gowenrw/sailor_moon_badge/art/inspiration/741863f426b0aff89c0e56212ef1270b.jpg

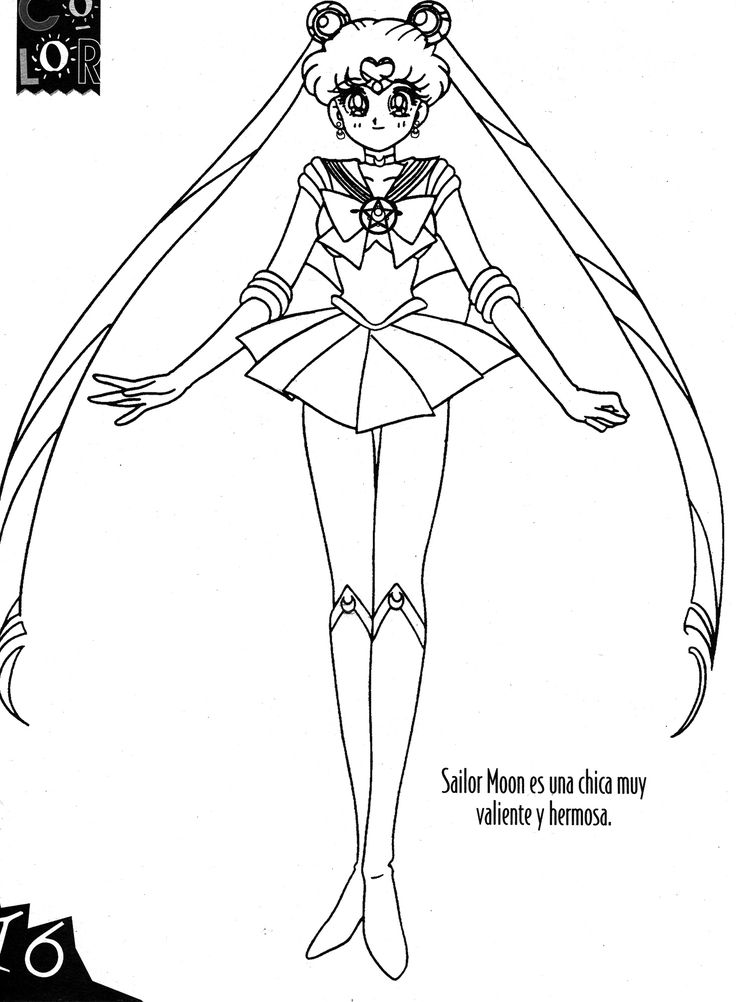
art/inspiration/741863f426b0aff89c0e56212ef1270b.jpg
