gowenrw/sailor_moon_badge/art/inspiration/3416023.png

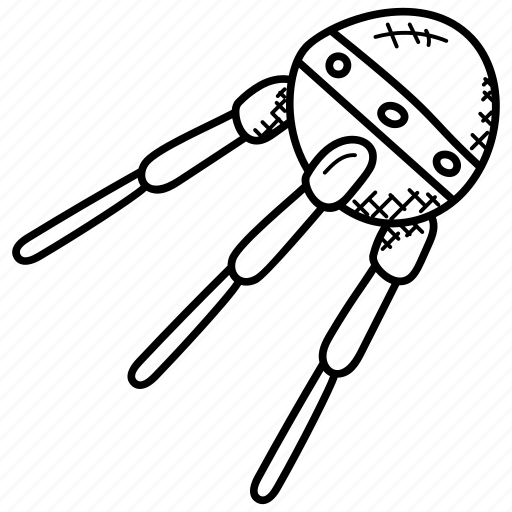
art/inspiration/3416023.png
