gowenrw/sailor_moon_badge/art/inspiration/aniyuki-sailor-moon-coloring-pages-17.jpg

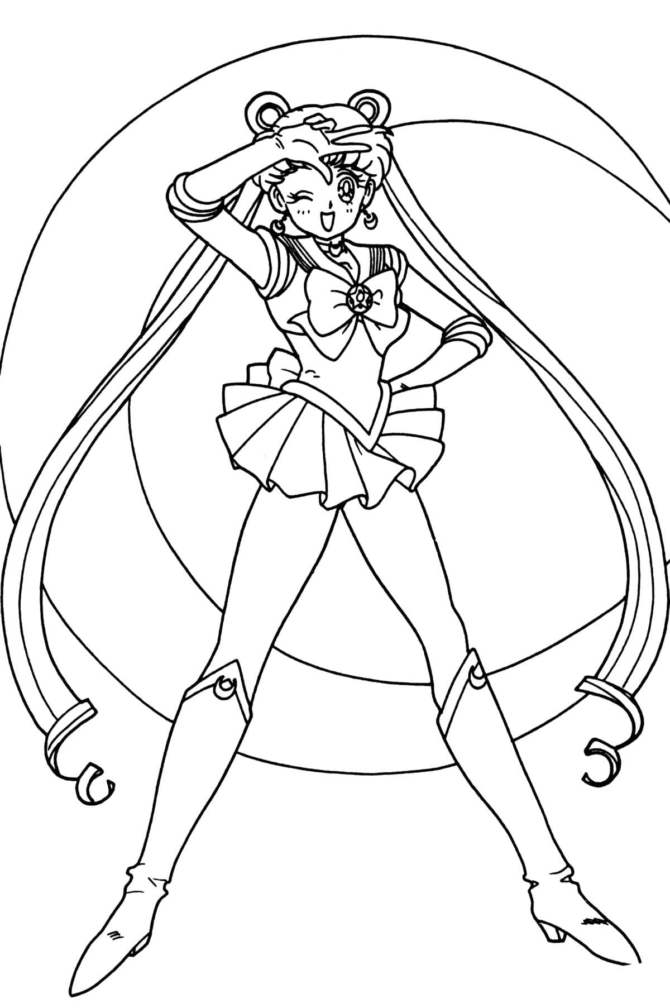
art/inspiration/aniyuki-sailor-moon-coloring-pages-17.jpg
