gowenrw/sailor_moon_badge/art/inspiration/earth.JPG

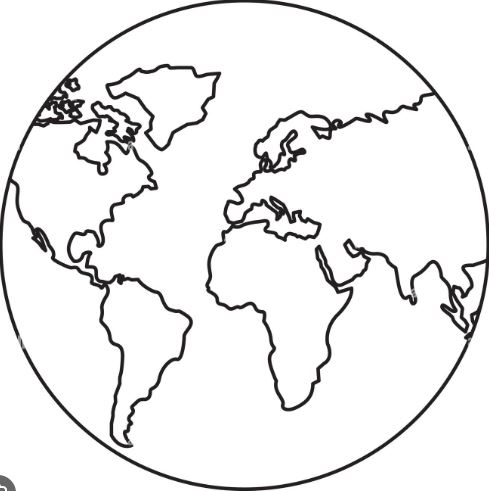
art/inspiration/earth.JPG
