gowenrw/sailor_moon_badge/art/inspiration/heart_wings.JPG

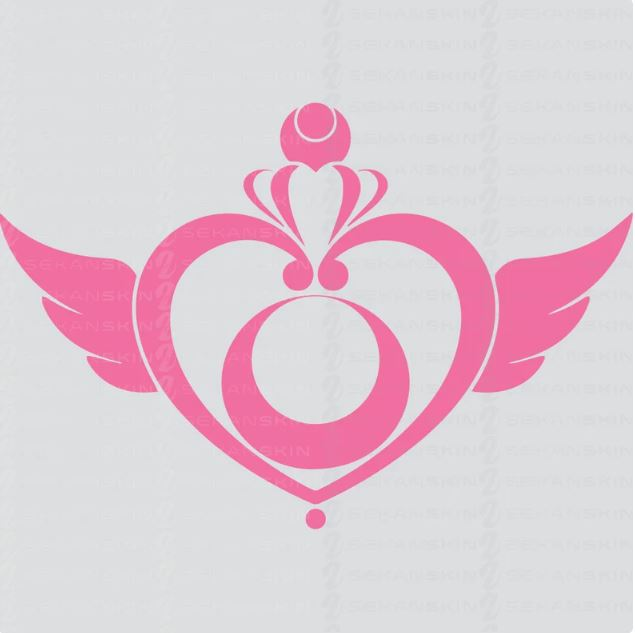
art/inspiration/heart_wings.JPG
