gowenrw/sailor_moon_badge/art/inspiration/il_fullxfull.png

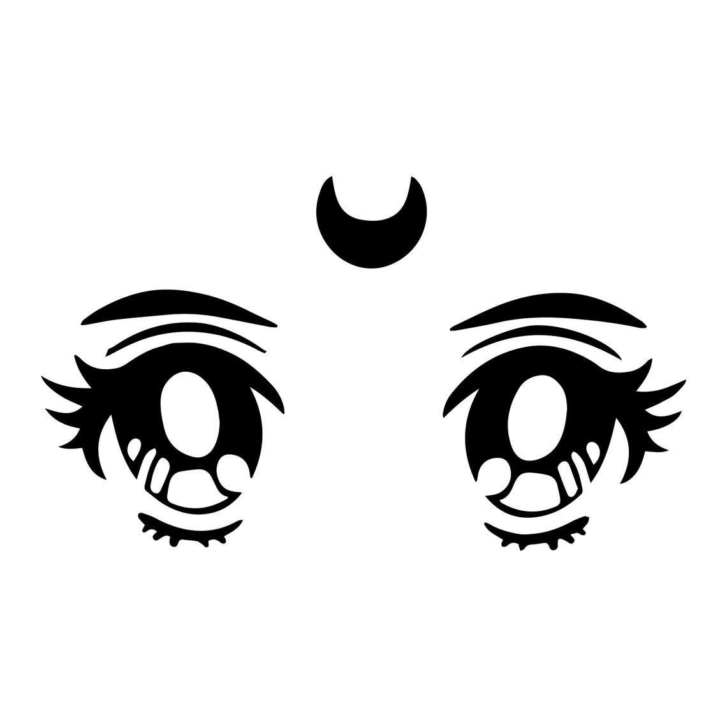
art/inspiration/il_fullxfull.png
