gowenrw/sailor_moon_badge/art/inspiration/Raskrasil.com-Sailor-Moon-2.jpg

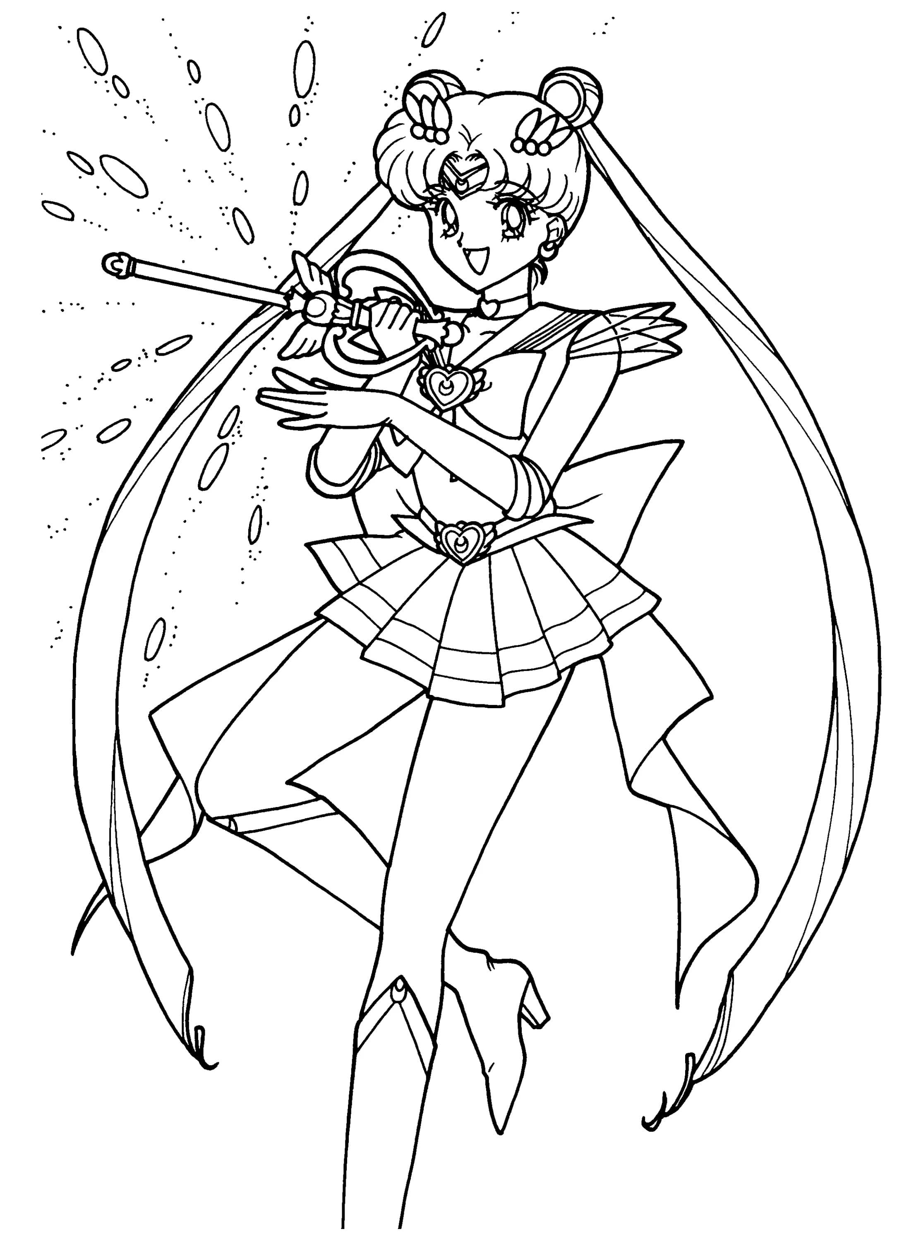
art/inspiration/Raskrasil.com-Sailor-Moon-2.jpg
