gowenrw/sailor_moon_badge/art/inspiration/sailor_moon_sketch_by_art_gives_me_purpose_dey1yrh-fullview.jpg

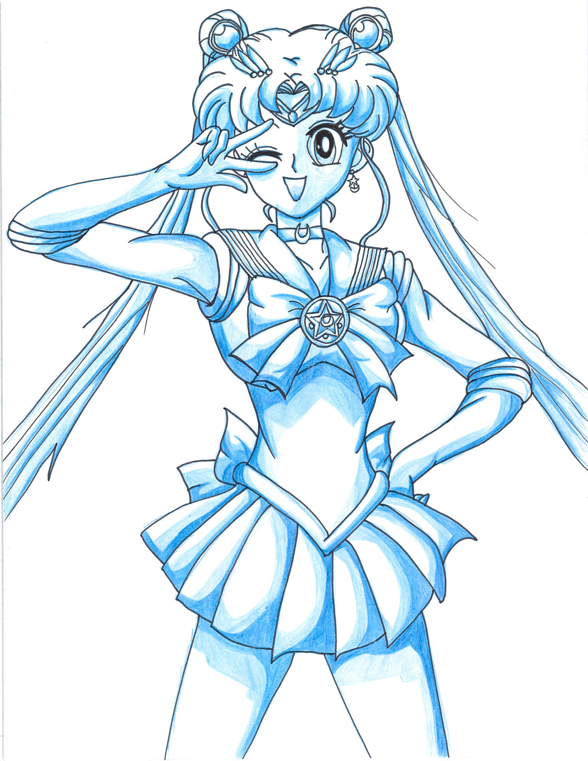
art/inspiration/sailor_moon_sketch_by_art_gives_me_purpose_dey1yrh-fullview.jpg
