gowenrw/sailor_moon_badge/art/inspiration/satellite.png

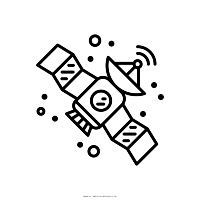
art/inspiration/satellite.png
