gowenrw/sailor_moon_badge/art/Sailor_Moon-1-maskb-01.jpg

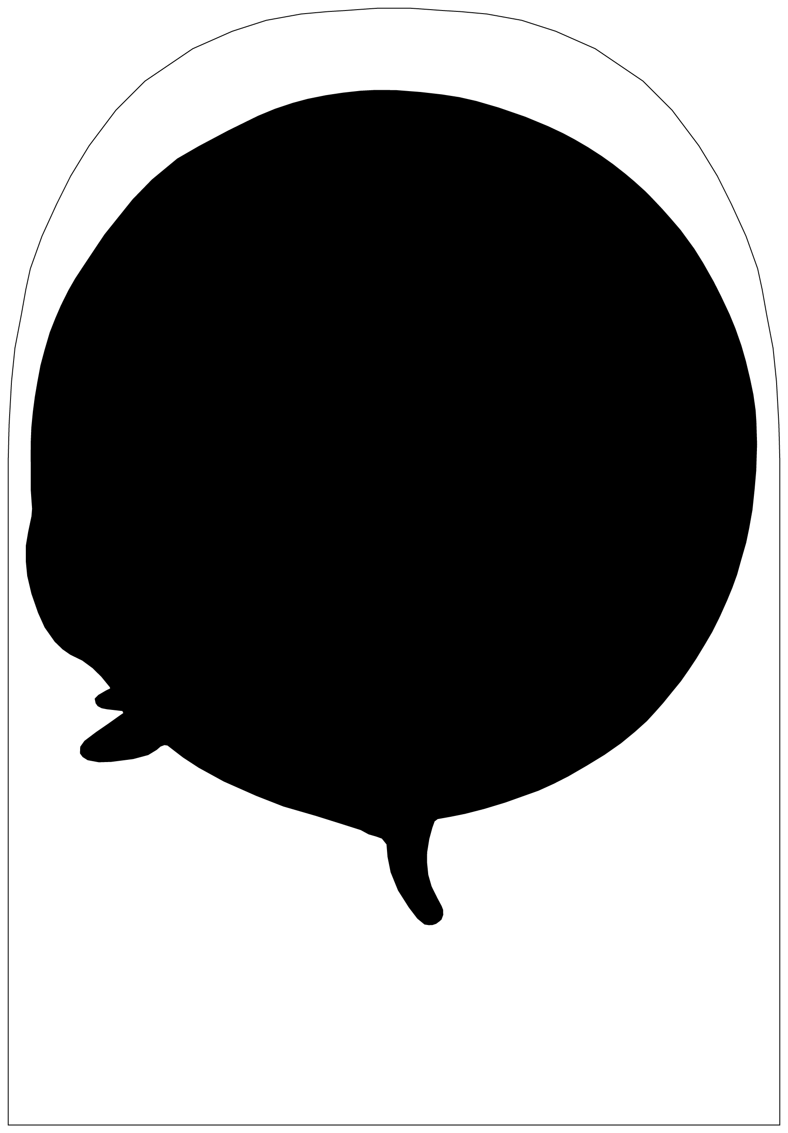
art/Sailor_Moon-1-maskb-01.jpg
