gowenrw/sailor_moon_badge/art/Sailor_Moon-1-maskf-01.jpg

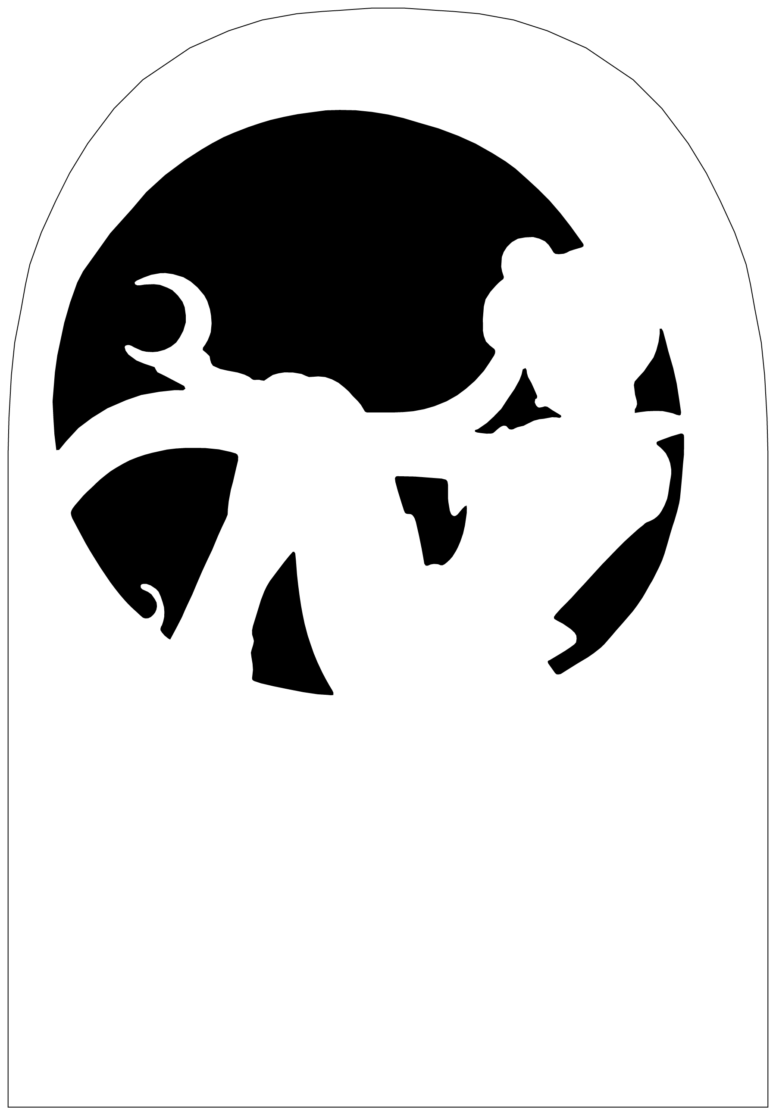
art/Sailor_Moon-1-maskf-01.jpg
