gowenrw/sailor_moon_badge/art/Sailor_Moon-2-bottom-01.jpg

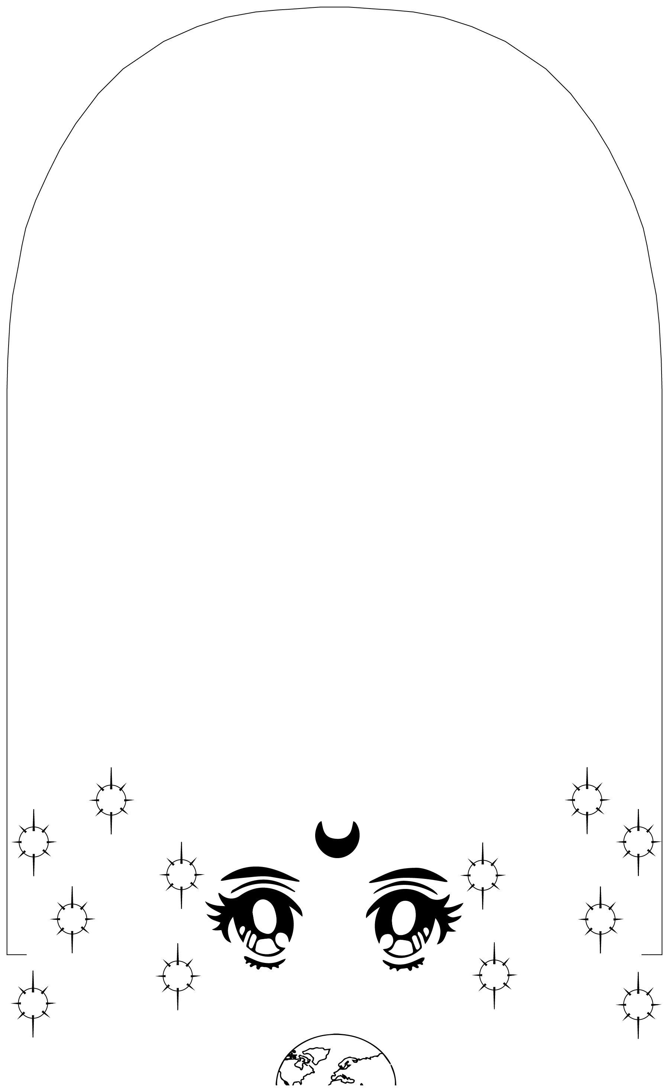
art/Sailor_Moon-2-bottom-01.jpg
