gowenrw/sailor_moon_badge/eda/sailor_moon/gerber/PCBWAY-DrillSettings.JPG

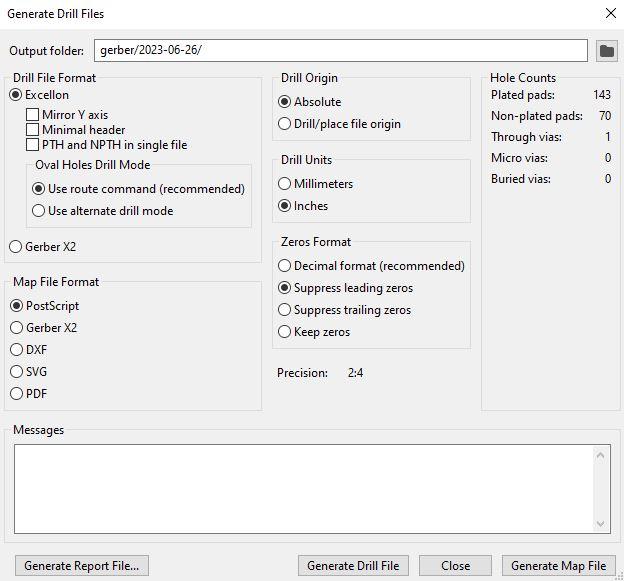
eda/sailor_moon/gerber/PCBWAY-DrillSettings.JPG
