gowenrw/sailor_moon_badge/eda/sailor_moon/gerber/PCBWAY-GerberSetting.JPG

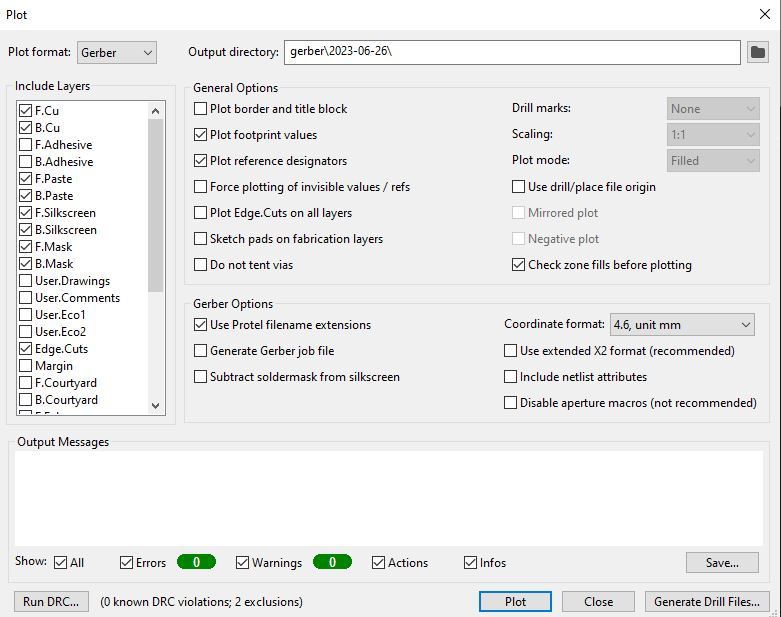
eda/sailor_moon/gerber/PCBWAY-GerberSetting.JPG
