gowenrw/sailor_moon_badge/eda/sailor_moon/snapshots/sailor_moon_3d_back.jpg

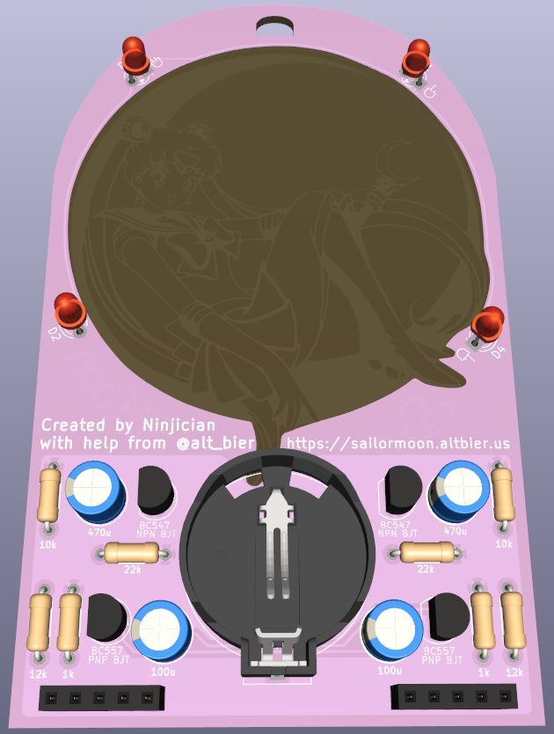
eda/sailor_moon/snapshots/sailor_moon_3d_back.jpg
