gowenrw/sailor_moon_badge/eda/sailor_moon/snapshots/sailor_moon_3d_front.jpg

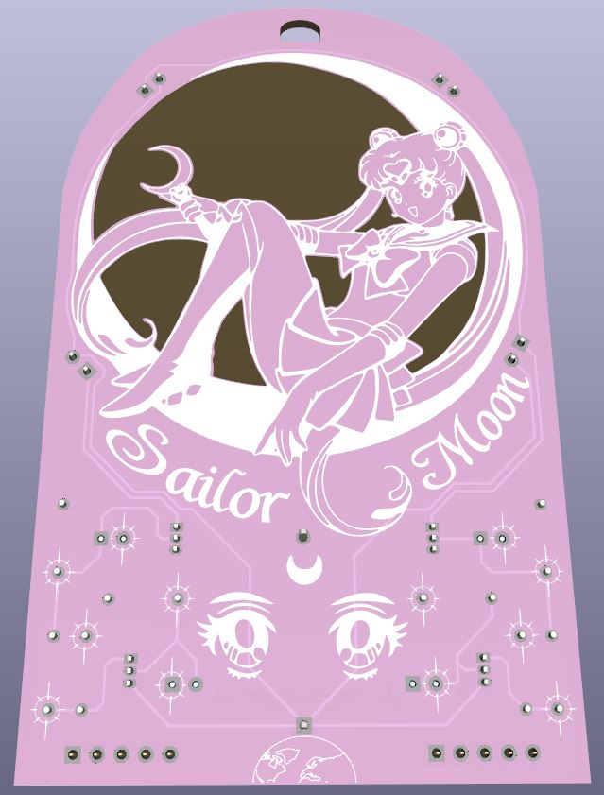
eda/sailor_moon/snapshots/sailor_moon_3d_front.jpg
