gowenrw/sailor_moon_badge/eda/sailor_moon/3d_models/PinHeader_1x02_P2.54mm_Horizontal.step

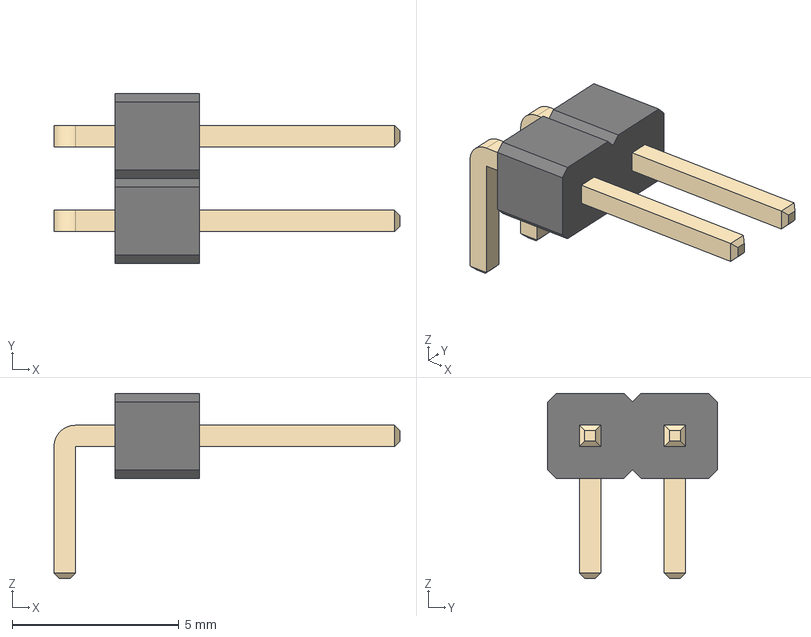
[picture p48: CAD file, 2023-08-03]
eda/sailor_moon/3d_models/PinHeader_1x02_P2.54mm_Horizontal.step
10.4 x 5.08 x 5.54 mm
