gowenrw/sailor_moon_badge/eda/sailor_moon/3d_models/LED_0805_2012Metric_Castellated.step

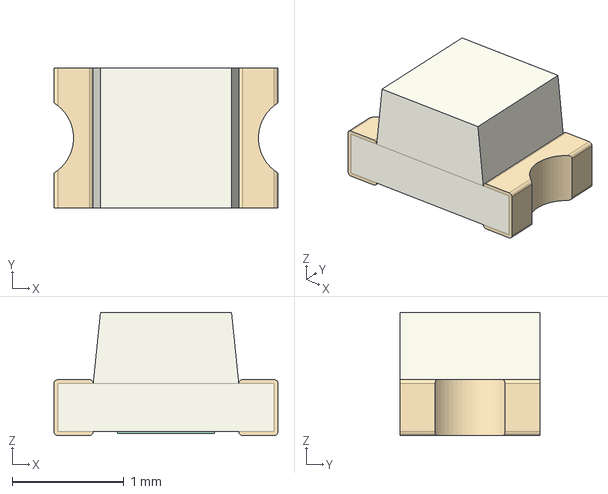
[picture p52: CAD file, 2023-08-03]
eda/sailor_moon/3d_models/LED_0805_2012Metric_Castellated.step
2.00 x 1.25 x 1.10 mm
