gowenrw/sailor_moon_badge/eda/sailor_moon/3d_models/R_Axial_DIN0207_L6.3mm_D2.5mm_P7.62mm_Horizontal.step

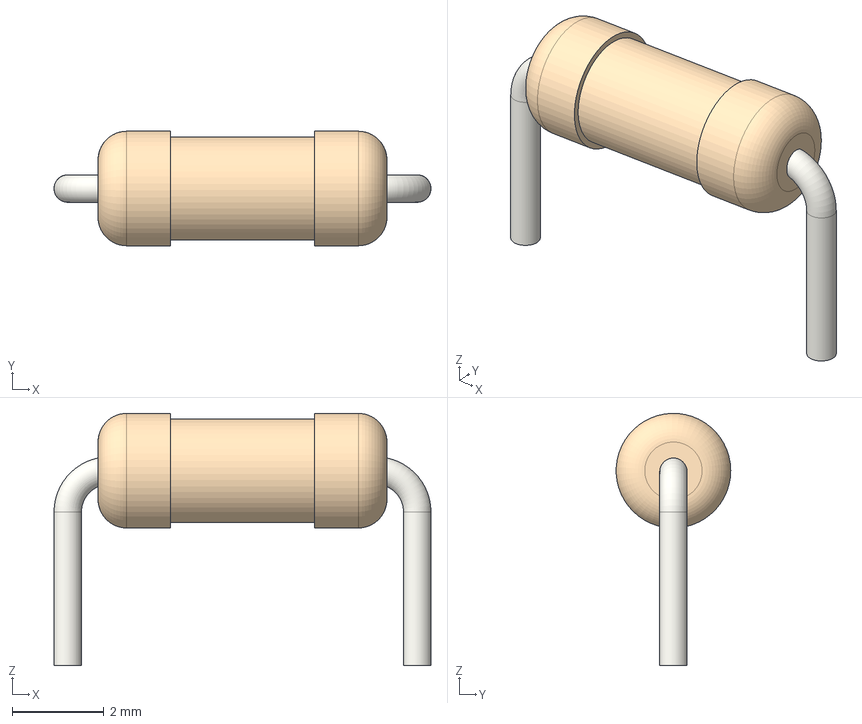
[picture p54: CAD file, 2023-08-03]
eda/sailor_moon/3d_models/R_Axial_DIN0207_L6.3mm_D2.5mm_P7.62mm_Horizontal.step
8.22 x 2.50 x 5.50 mm
