gowenrw/sailor_moon_badge/eda/sailor_moon/3d_models/LED_D5.0mm.step

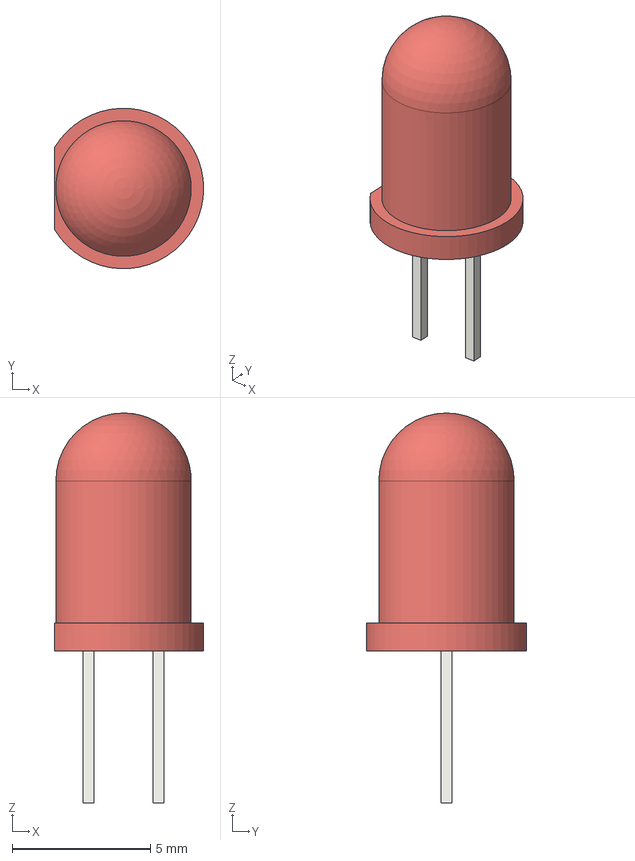
[picture p56: CAD file, 2023-08-03]
eda/sailor_moon/3d_models/LED_D5.0mm.step
5.40 x 5.79 x 14.1 mm
