gowenrw/sailor_moon_badge/eda/sailor_moon/3d_models/R_Axial_DIN0204_L3.6mm_D1.6mm_P5.08mm_Horizontal.step

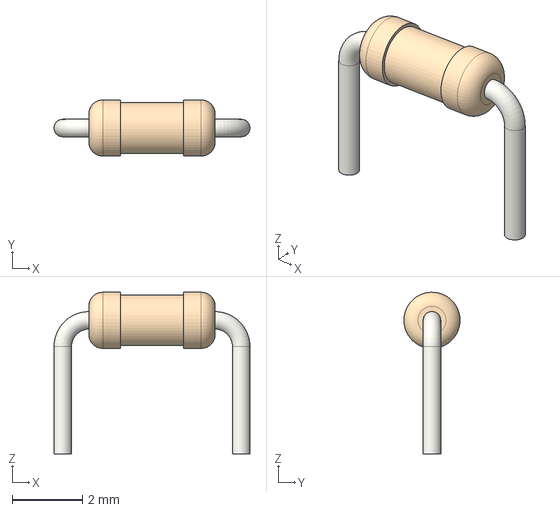
[picture p58: CAD file, 2023-08-03]
eda/sailor_moon/3d_models/R_Axial_DIN0204_L3.6mm_D1.6mm_P5.08mm_Horizontal.step
5.58 x 1.60 x 4.60 mm
