gowenrw/sailor_moon_badge/eda/sailor_moon/3d_models/CUI_PXO7803-500-M-TR.step

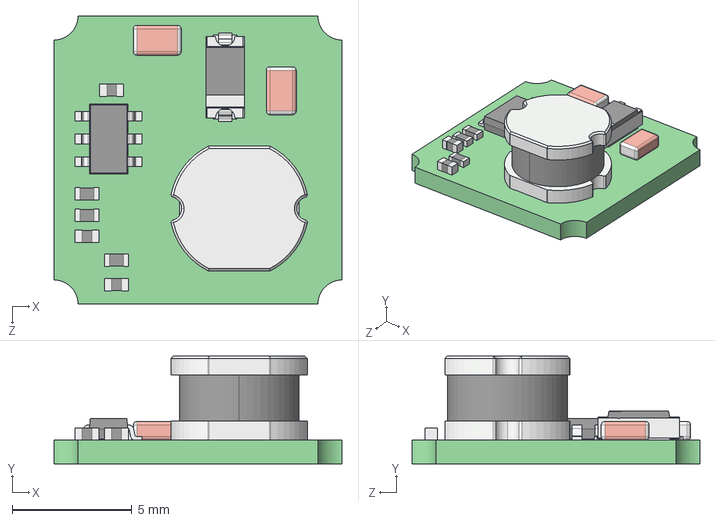
[picture p61: CAD file, 2023-08-03]
eda/sailor_moon/3d_models/CUI_PXO7803-500-M-TR.step
12.0 x 4.50 x 12.0 mm
