gowenrw/sailor_moon_badge/eda/sailor_moon/3d_models/PinSocket_1x04_P2.54mm_Horizontal.step

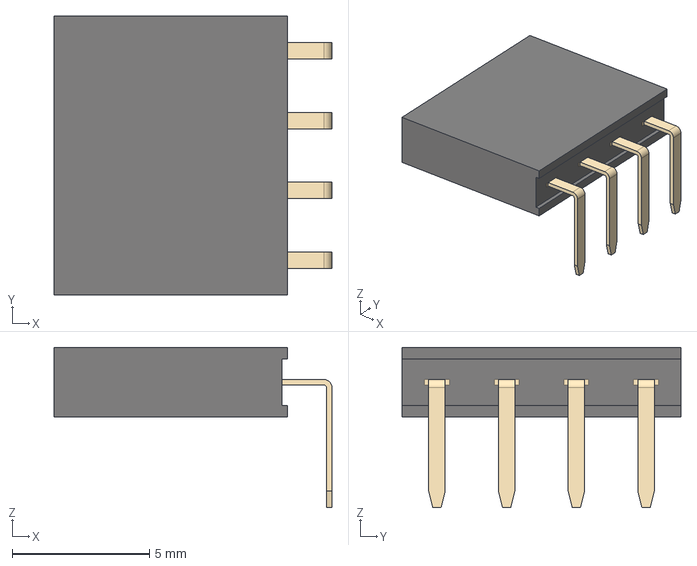
[picture p65: CAD file, 2023-08-03]
eda/sailor_moon/3d_models/PinSocket_1x04_P2.54mm_Horizontal.step
10.1 x 10.2 x 5.84 mm
