gowenrw/sailor_moon_badge/eda/sailor_moon/3d_models/C_1206_3216Metric.step

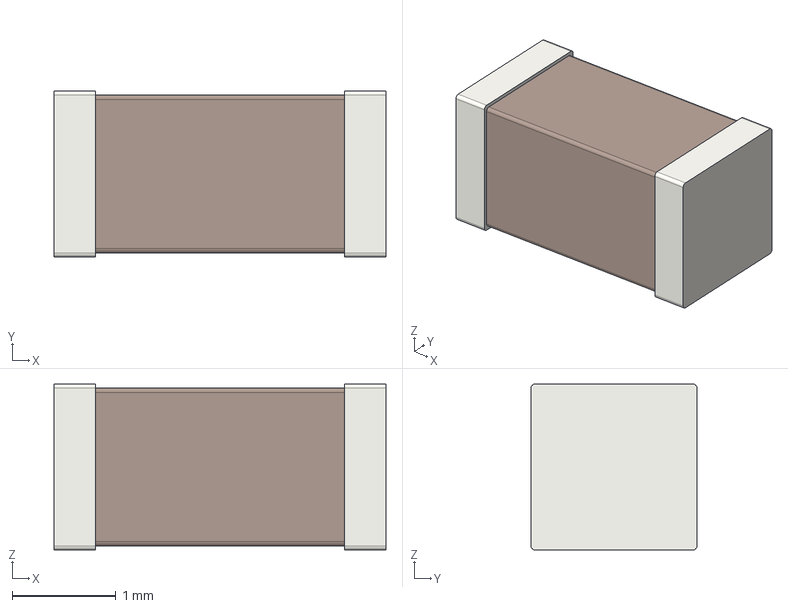
[picture p66: CAD file, 2023-08-03]
eda/sailor_moon/3d_models/C_1206_3216Metric.step
3.20 x 1.60 x 1.60 mm
