gowenrw/sailor_moon_badge/eda/sailor_moon/3d_models/LED_D3.0mm.step

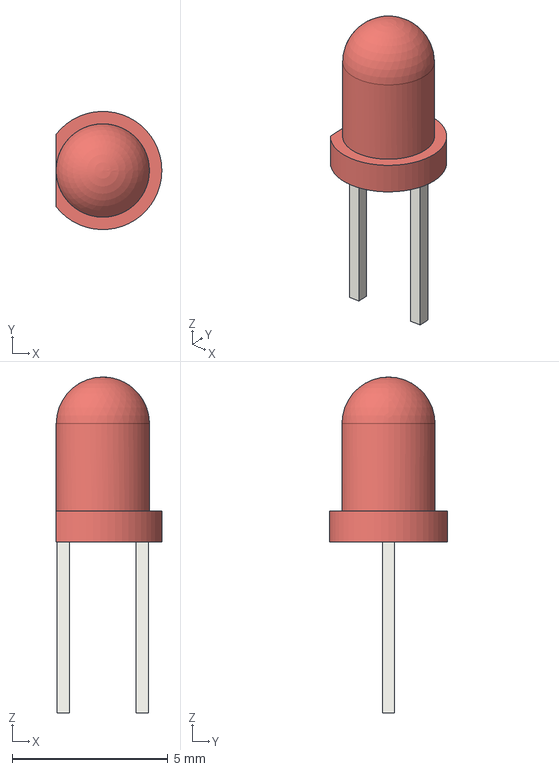
[picture p68: CAD file, 2023-08-03]
eda/sailor_moon/3d_models/LED_D3.0mm.step
3.40 x 3.80 x 10.8 mm
