gowenrw/sailor_moon_badge/eda/sailor_moon/3d_models/SW_SPDT_PCM12.step

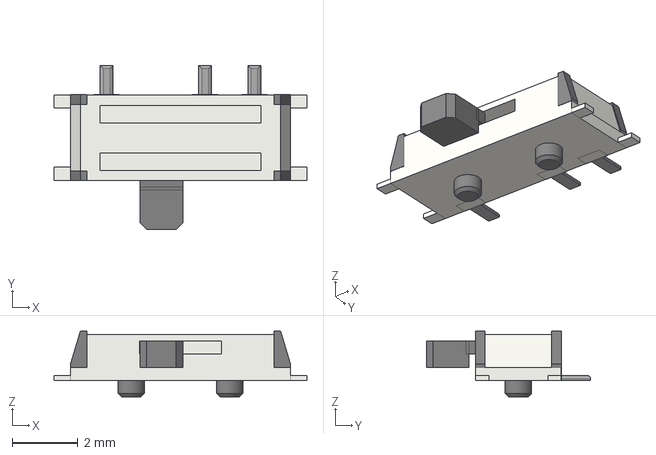
[picture p70: CAD file, 2023-08-03]
eda/sailor_moon/3d_models/SW_SPDT_PCM12.step
7.70 x 5.00 x 2.00 mm
