gowenrw/sailor_moon_badge/eda/sailor_moon/3d_models/RJ45_Amphenol_RJHSE-5080-56544.STEP

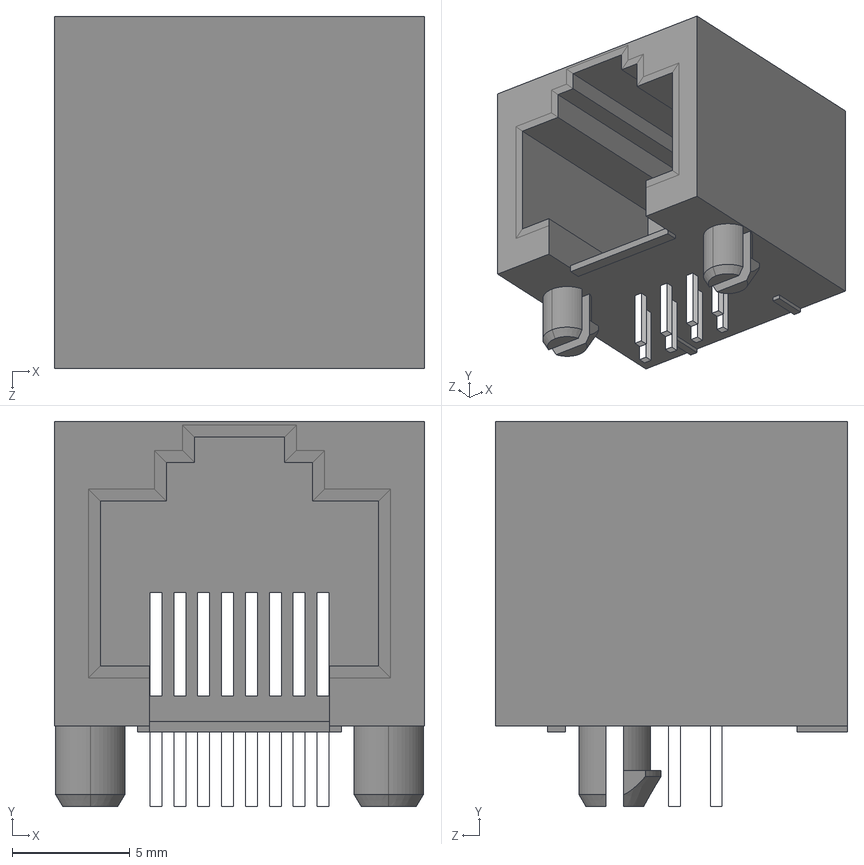
[picture p72: CAD file, 2023-08-03]
eda/sailor_moon/3d_models/RJ45_Amphenol_RJHSE-5080-56544.STEP
15.7 x 16.4 x 15.0 mm
