gowenrw/sailor_moon_badge/eda/sailor_moon/3d_models/Battery_Holder_CR2032_BS-2-1.stp

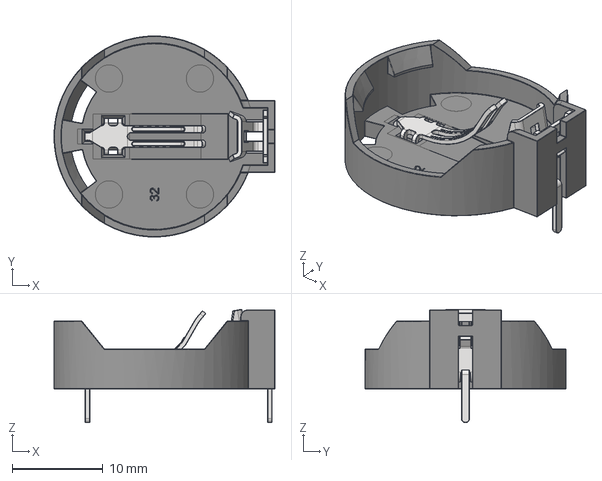
[picture p73: CAD file, 2023-08-03]
eda/sailor_moon/3d_models/Battery_Holder_CR2032_BS-2-1.stp
24.3 x 22.1 x 12.5 mm
