gowenrw/sailor_moon_badge/eda/sailor_moon/3d_models/TO-92_Inline.step

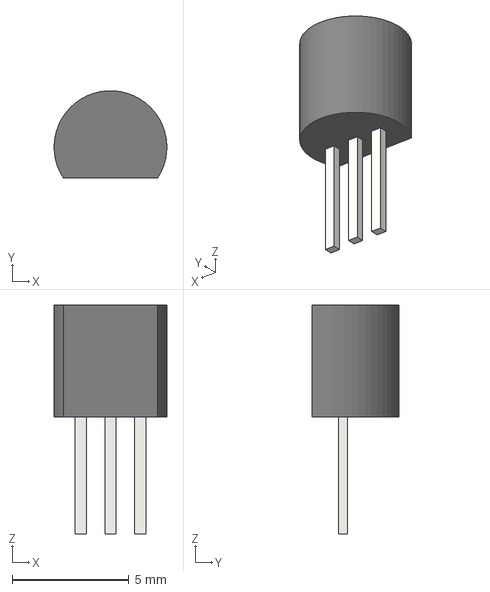
[picture p78: CAD file, 2023-08-03]
eda/sailor_moon/3d_models/TO-92_Inline.step
4.83 x 3.74 x 9.80 mm
