gowenrw/sailor_moon_badge/eda/sailor_moon/3d_models/TS2306A.step

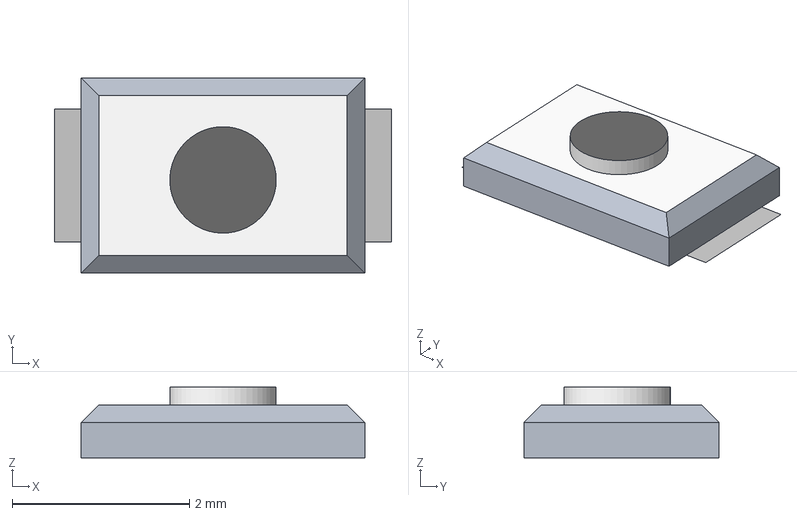
[picture p79: CAD file, 2023-08-03]
eda/sailor_moon/3d_models/TS2306A.step
3.80 x 2.20 x 0.8 mm
Plane
