gowenrw/sailor_moon_badge/eda/sailor_moon/3d_models/PinSocket_1x03_P2.54mm_Vertical.step

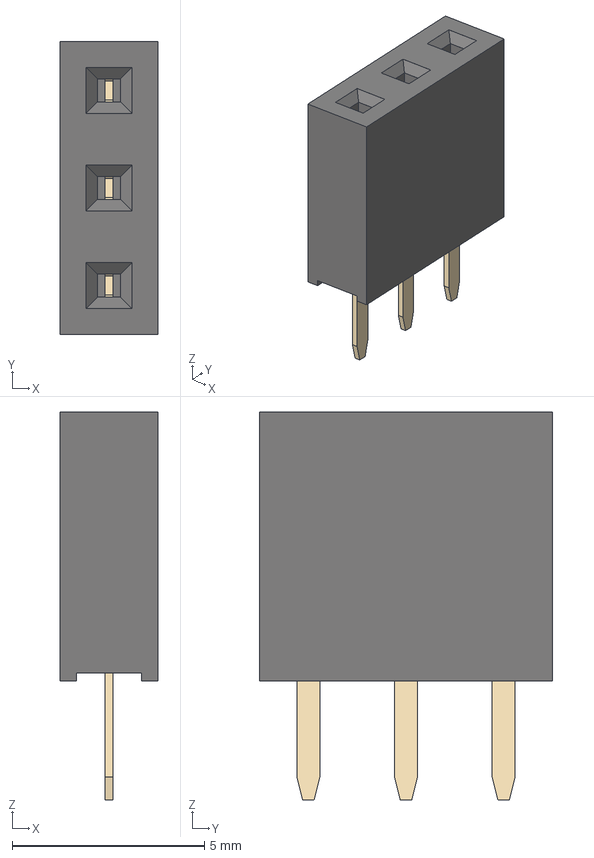
[picture p83: CAD file, 2023-08-03]
eda/sailor_moon/3d_models/PinSocket_1x03_P2.54mm_Vertical.step
2.54 x 7.62 x 10.1 mm
