gowenrw/sailor_moon_badge/eda/sailor_moon/3d_models/Battery_Holder_3xAAA_Simple.step

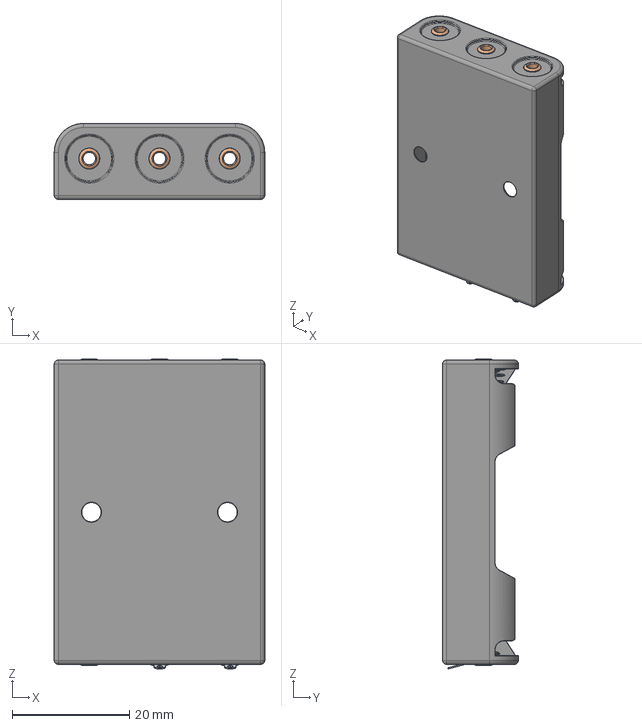
[picture p85: CAD file, 2023-08-03]
eda/sailor_moon/3d_models/Battery_Holder_3xAAA_Simple.step
36.0 x 13.0 x 53.0 mm
