gowenrw/sailor_moon_badge/eda/sailor_moon/3d_models/PinSocket_1x20_P2.54mm_Horizontal.step

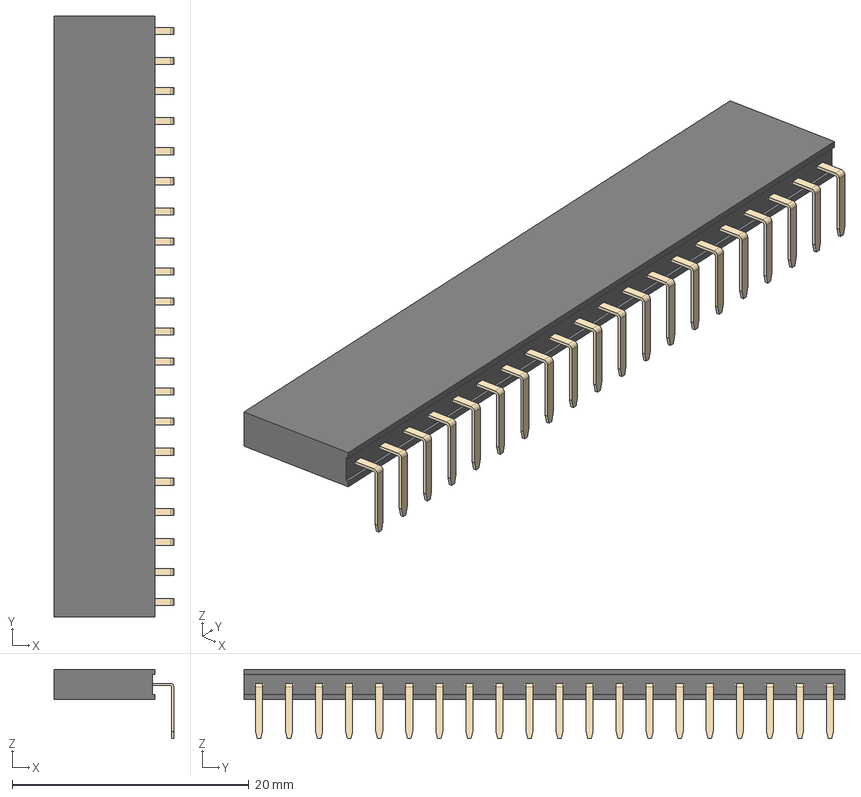
[picture p89: CAD file, 2023-08-03]
eda/sailor_moon/3d_models/PinSocket_1x20_P2.54mm_Horizontal.step
10.1 x 50.8 x 5.84 mm
