gowenrw/sailor_moon_badge/eda/sailor_moon/3d_models/LED_1206_3216Metric_Castellated.step

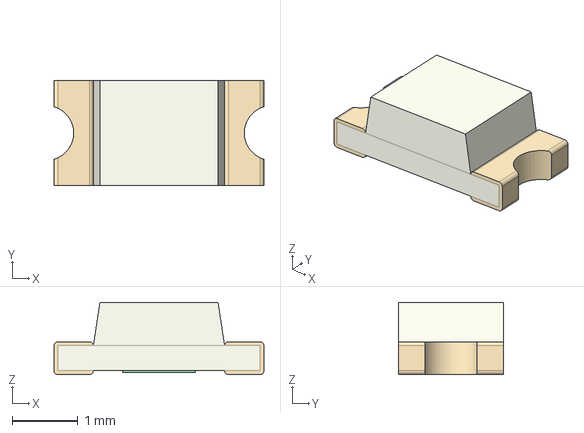
[picture p90: CAD file, 2023-08-03]
eda/sailor_moon/3d_models/LED_1206_3216Metric_Castellated.step
3.20 x 1.60 x 1.10 mm
