gowenrw/sailor_moon_badge/eda/sailor_moon/3d_models/PinHeader_1x09_P2.54mm_Vertical.step

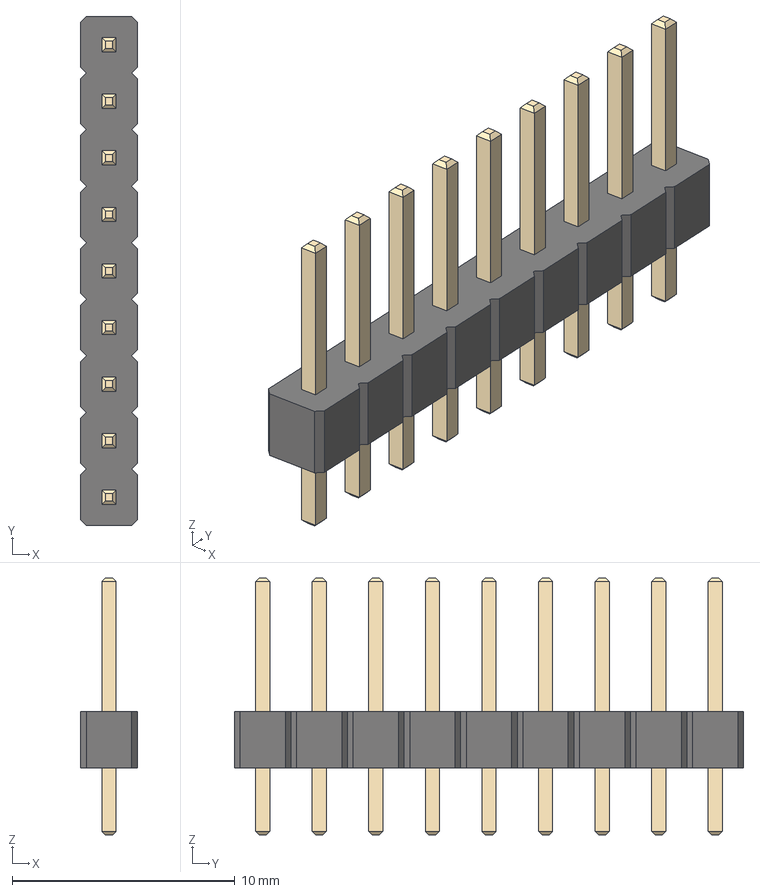
[picture p94: CAD file, 2023-08-03]
eda/sailor_moon/3d_models/PinHeader_1x09_P2.54mm_Vertical.step
2.54 x 22.9 x 11.5 mm
