gowenrw/sailor_moon_badge/eda/sailor_moon/3d_models/USB_Micro-B_Molex_47346-0001.step

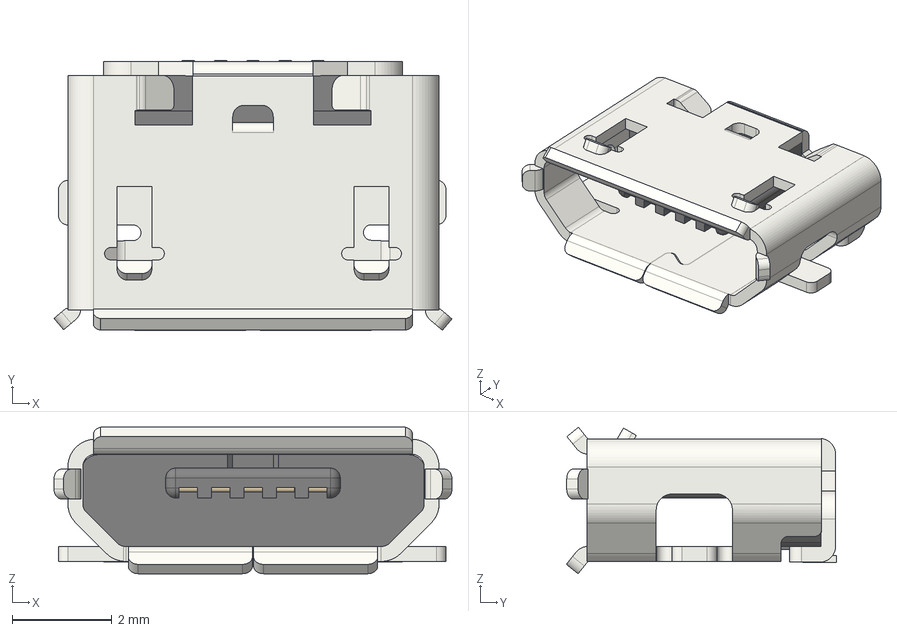
[picture p98: CAD file, 2023-08-03]
eda/sailor_moon/3d_models/USB_Micro-B_Molex_47346-0001.step
7.98 x 5.42 x 2.94 mm
