gowenrw/sailor_moon_badge/eda/sailor_moon/3d_models/LED_D8.0mm.step

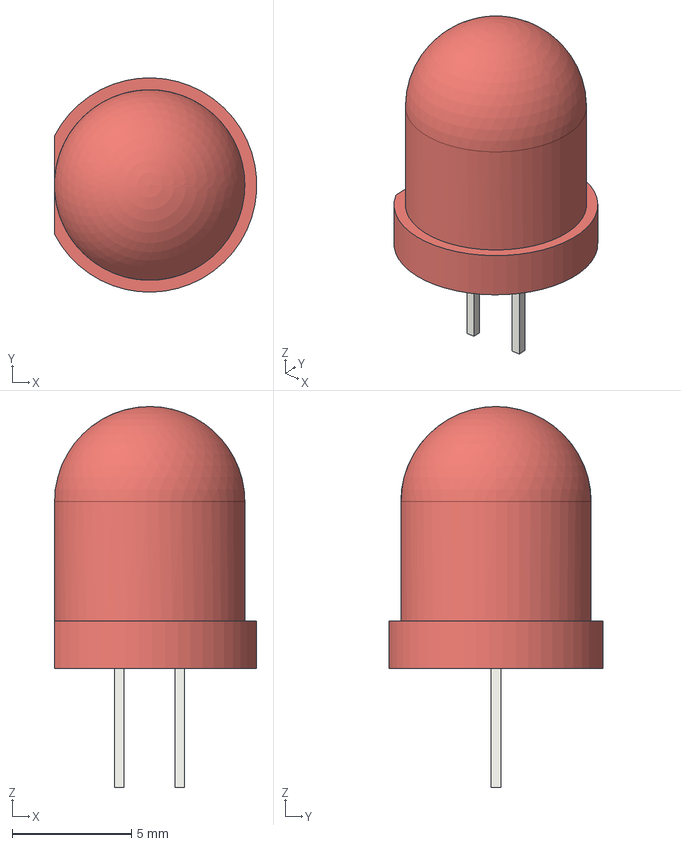
[picture p99: CAD file, 2023-08-03]
eda/sailor_moon/3d_models/LED_D8.0mm.step
8.49 x 9.00 x 16.0 mm
