gowenrw/sailor_moon_badge/eda/sailor_moon/3d_models/R_0603_1608Metric.step

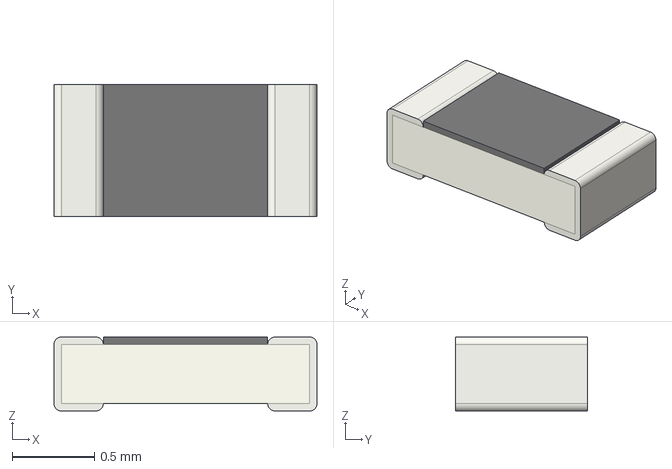
[picture p100: CAD file, 2023-08-03]
eda/sailor_moon/3d_models/R_0603_1608Metric.step
1.60 x 0.8 x 0.45 mm
