gowenrw/sailor_moon_badge/eda/sailor_moon/3d_models/SOT-23.step

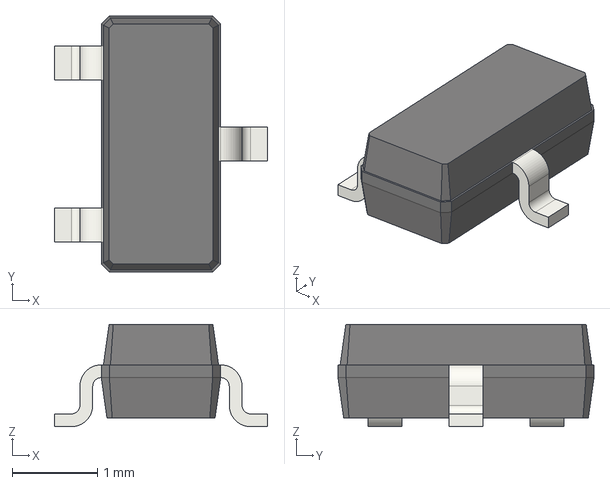
[picture p103: CAD file, 2023-08-03]
eda/sailor_moon/3d_models/SOT-23.step
2.50 x 3.00 x 1.20 mm
