gowenrw/sailor_moon_badge/eda/sailor_moon/3d_models/C_0805_2012Metric.step

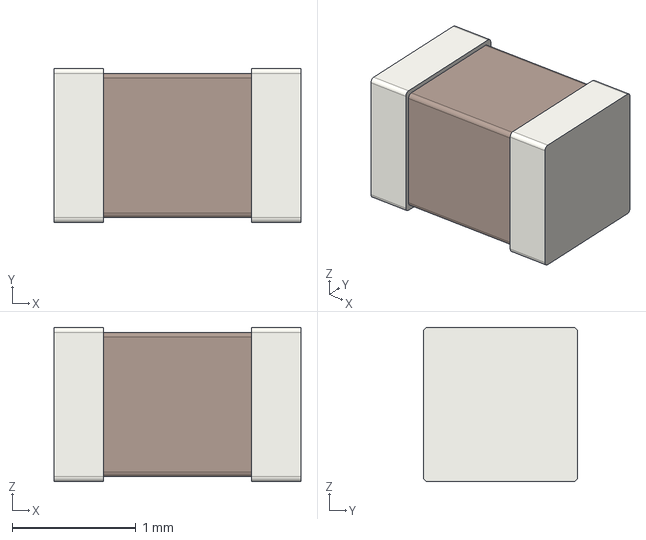
[picture p104: CAD file, 2023-08-03]
eda/sailor_moon/3d_models/C_0805_2012Metric.step
2.00 x 1.25 x 1.25 mm
