gowenrw/sailor_moon_badge/eda/sailor_moon/3d_models/R_0805_2012Metric.step

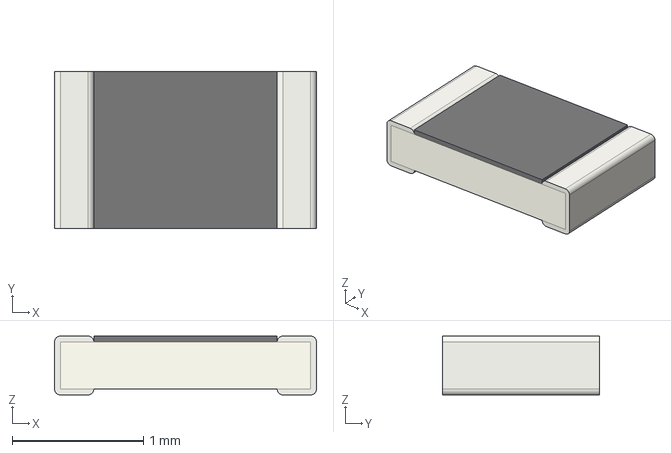
[picture p105: CAD file, 2023-08-03]
eda/sailor_moon/3d_models/R_0805_2012Metric.step
2.00 x 1.20 x 0.45 mm
