gowenrw/sailor_moon_badge/eda/sailor_moon/3d_models/LED_D3.0mm-3.step

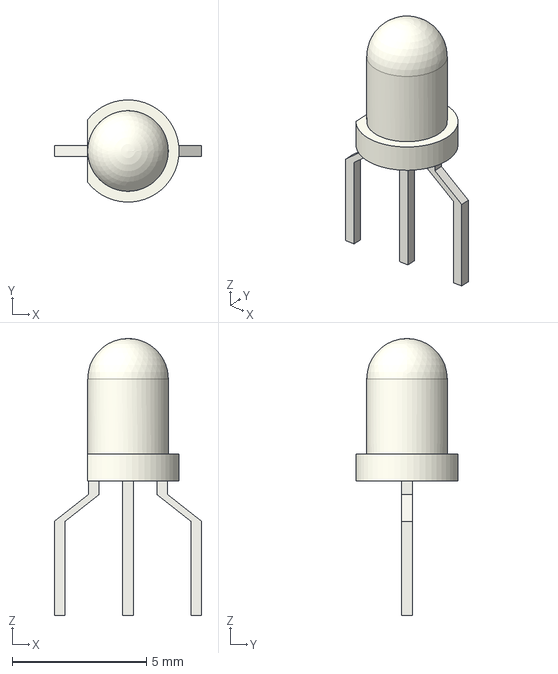
[picture p106: CAD file, 2023-08-03]
eda/sailor_moon/3d_models/LED_D3.0mm-3.step
5.48 x 3.80 x 10.3 mm
