gowenrw/sailor_moon_badge/eda/sailor_moon/3d_models/SOIC-16_3.9x9.9mm_P1.27mm.step

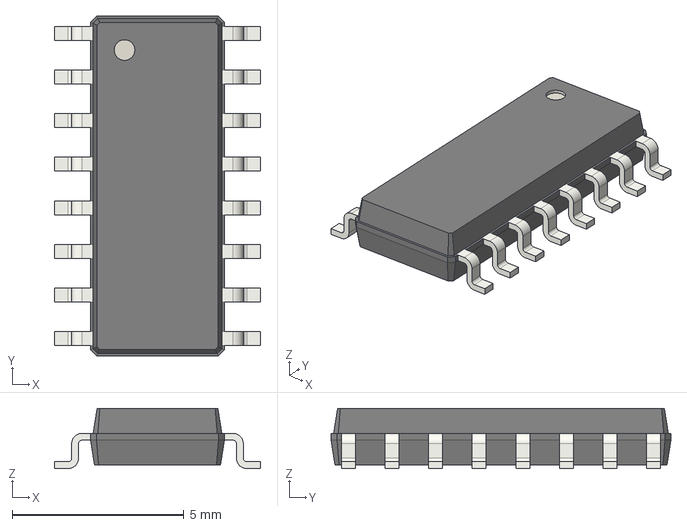
[picture p107: CAD file, 2023-08-03]
eda/sailor_moon/3d_models/SOIC-16_3.9x9.9mm_P1.27mm.step
6.00 x 9.90 x 1.75 mm
