gowenrw/sailor_moon_badge/eda/sailor_moon/3d_models/C_Disc_D3.0mm_W2.0mm_P2.50mm.step

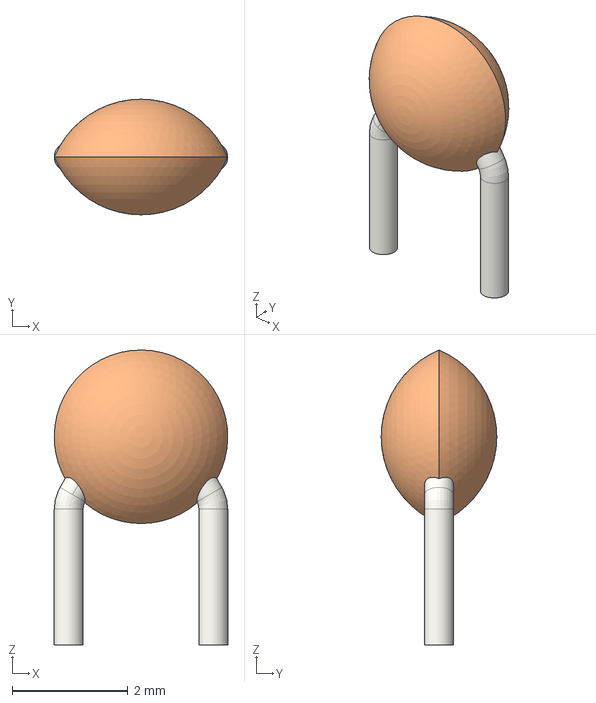
[picture p109: CAD file, 2023-08-03]
eda/sailor_moon/3d_models/C_Disc_D3.0mm_W2.0mm_P2.50mm.step
3.00 x 2.00 x 5.10 mm
