gowenrw/sailor_moon_badge/eda/sailor_moon/3d_models/RJ45_Amphenol_RJHSE538X.step

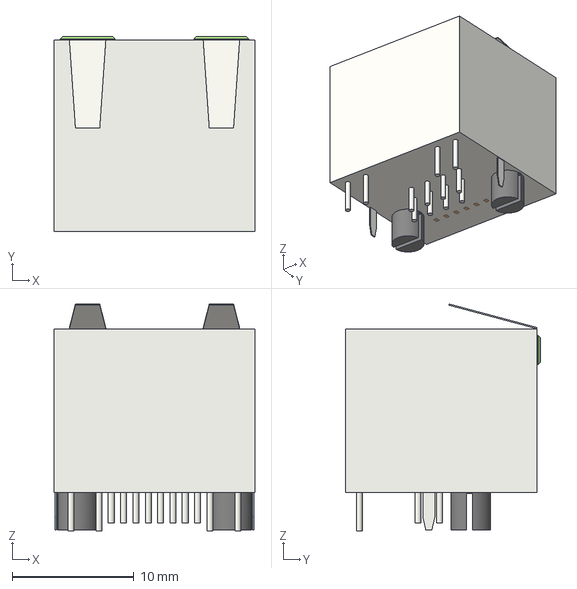
[picture p110: CAD file, 2023-08-03]
eda/sailor_moon/3d_models/RJ45_Amphenol_RJHSE538X.step
16.5 x 16.1 x 18.7 mm
