gowenrw/sailor_moon_badge/eda/sailor_moon/3d_models/BatteryHolder_2466_1xAAA.step

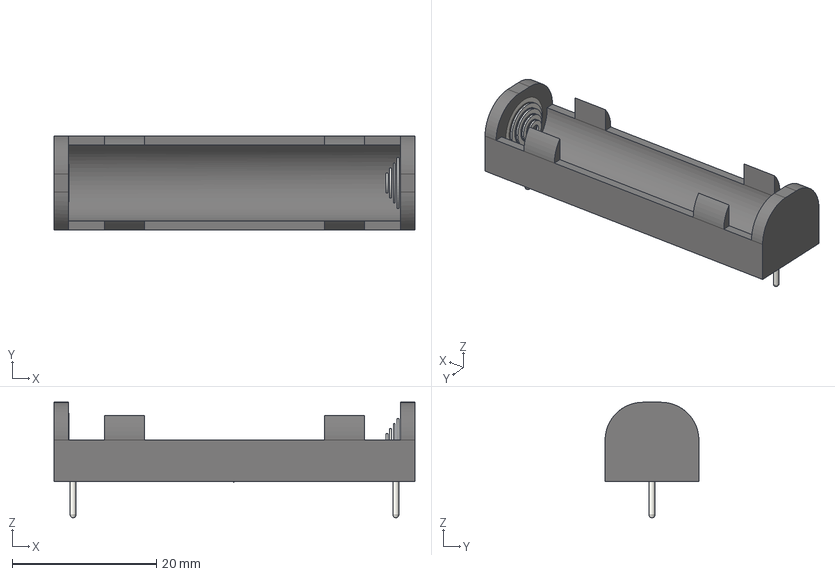
[picture p111: CAD file, 2023-08-03]
eda/sailor_moon/3d_models/BatteryHolder_2466_1xAAA.step
50.0 x 13.0 x 16.0 mm
