gowenrw/sailor_moon_badge/eda/sailor_moon/3d_models/CP_Radial_D5.0mm_P2.00mm.step

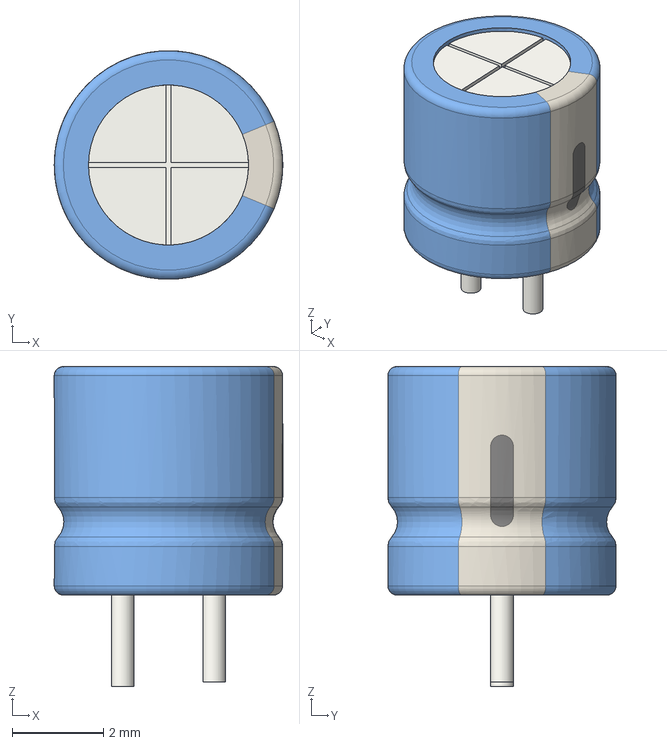
[picture p112: CAD file, 2023-08-03]
eda/sailor_moon/3d_models/CP_Radial_D5.0mm_P2.00mm.step
5.00 x 5.00 x 7.00 mm
