gowenrw/sailor_moon_badge/eda/sailor_moon/3d_models/CP_Radial_D6.3mm_P2.50mm.step

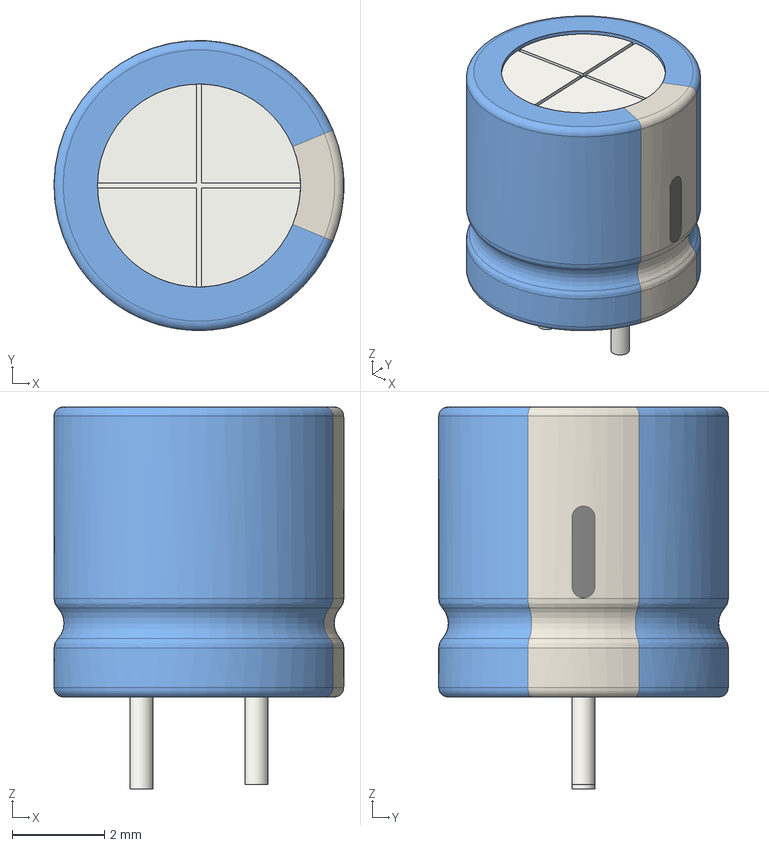
[picture p113: CAD file, 2023-08-03]
eda/sailor_moon/3d_models/CP_Radial_D6.3mm_P2.50mm.step
6.30 x 6.30 x 8.30 mm
