gowenrw/sailor_moon_badge/eda/sailor_moon/3d_models/PinSocket_1x08_P2.54mm_Vertical.step

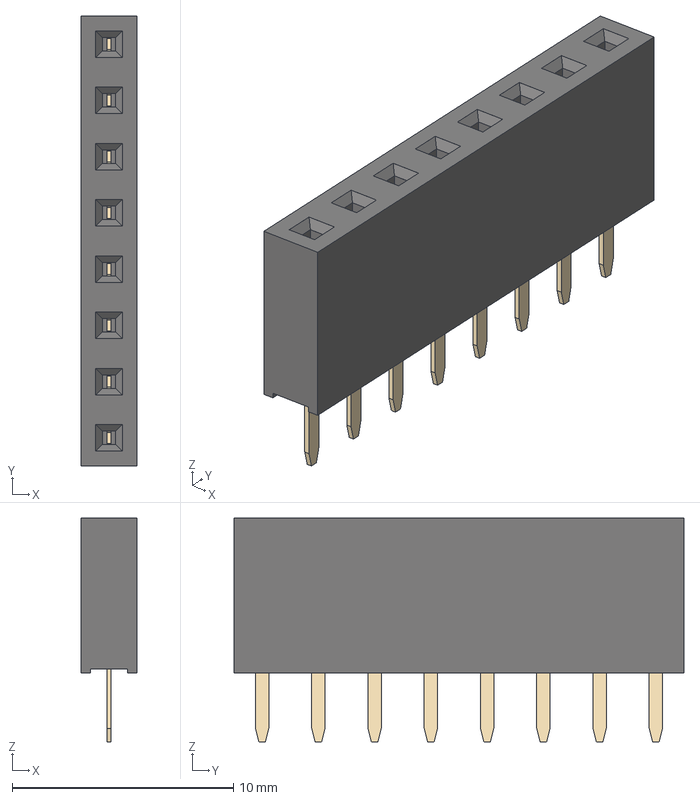
[picture p114: CAD file, 2023-08-03]
eda/sailor_moon/3d_models/PinSocket_1x08_P2.54mm_Vertical.step
2.54 x 20.3 x 10.1 mm
